isacben/picocade/kicad/picocade.kicad_sch

## KiCad design kicad/picocade.kicad_sch (2024-02-25, an earlier design)

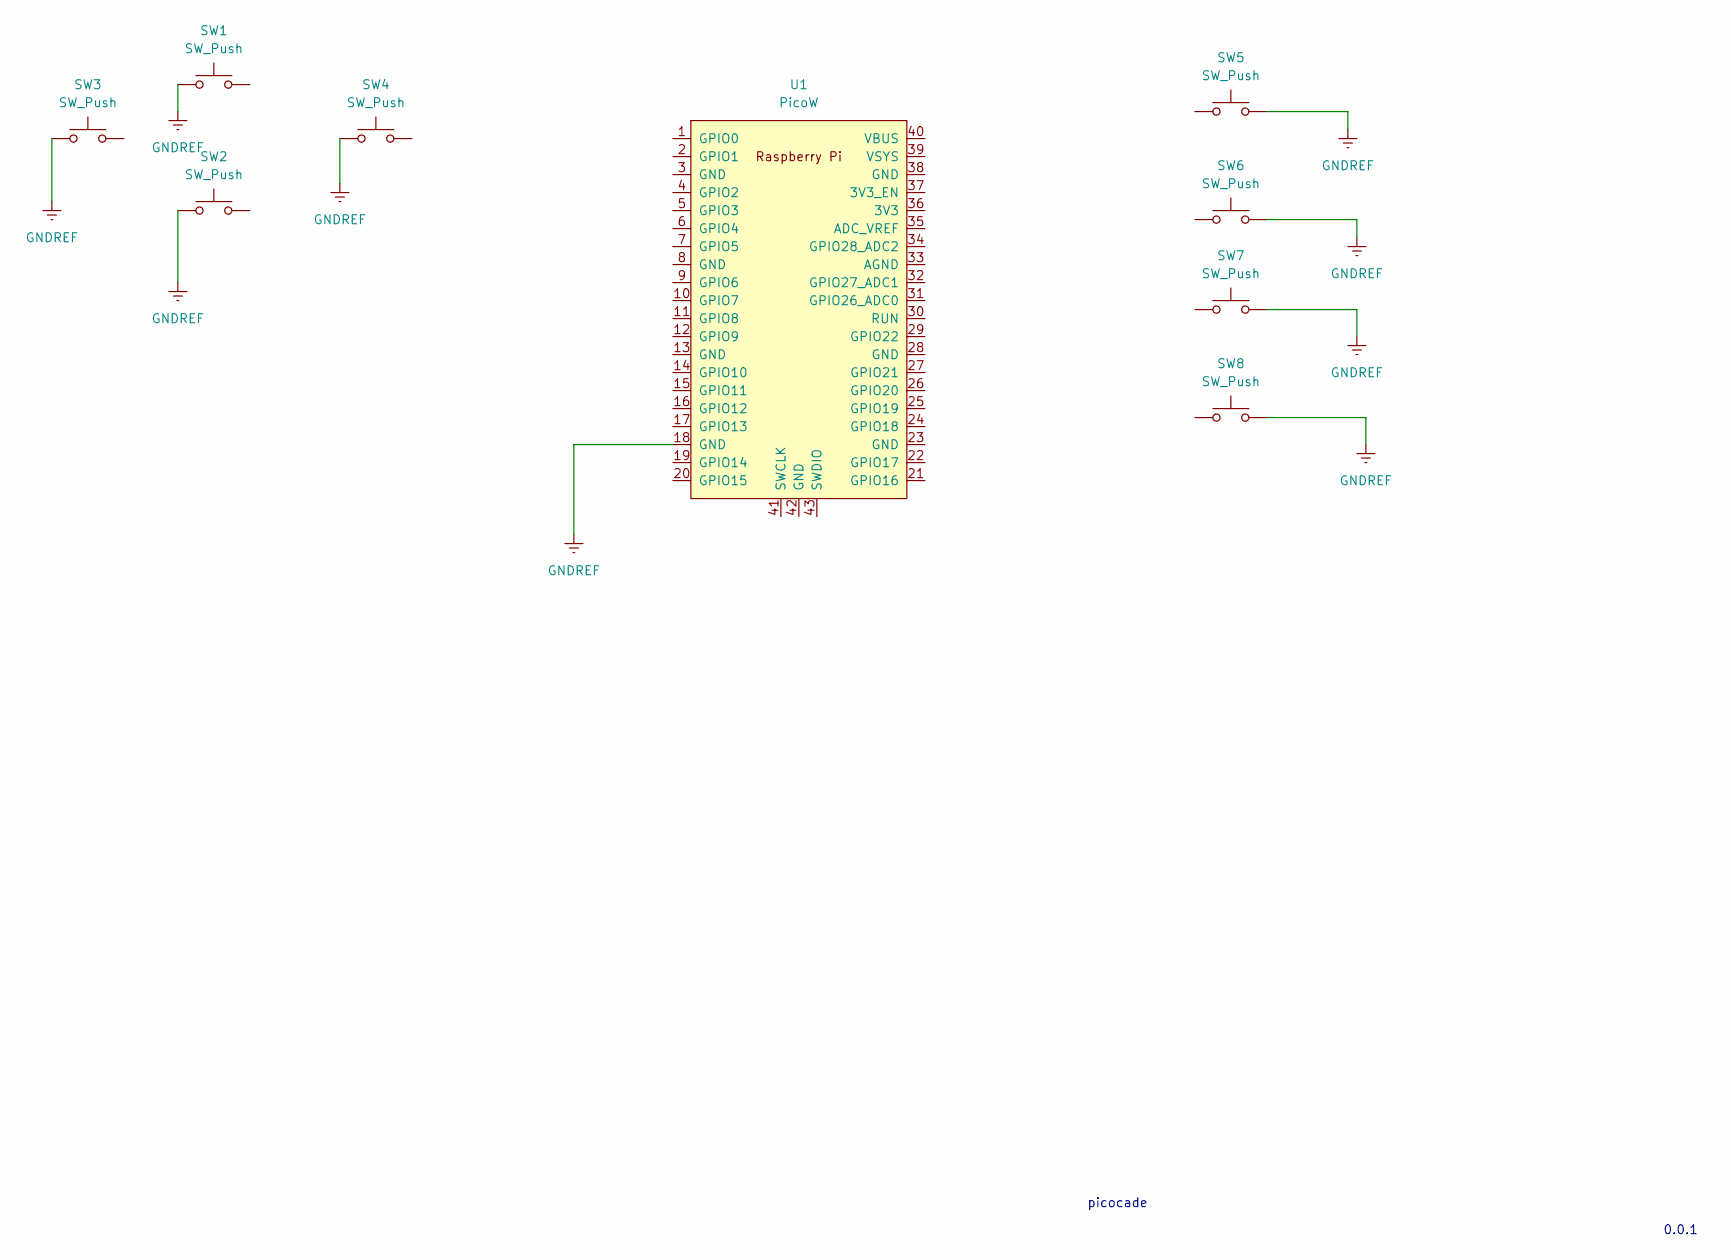
[picture p17: schematic picocade.kicad_sch]

Parts:
SW1, SW2, SW3, SW4, SW5, SW6, SW7, SW8: SW_Push
U1: PicoW; RPi_Pico_SMD_TH

Connections:
GNDREF: SW1.1, SW2.1, SW3.1, SW4.1, SW5.2, SW6.2, SW7.2, SW8.2, U1.18 (GND)

Notes on the sheet:
picocade
0.0.1
